evarty/7SegClock/ShiftOut.c

#include <avr/io.h>

#include "ShiftOut.h"

void ShiftOutByte(uint8_t CLKPin, volatile uint8_t *ClockPORT, uint8_t DataPin, volatile uint8_t *DataPORT, uint8_t LatchPin, volatile uint8_t *LatchPORT, uint8_t data){
  
  *LatchPORT &= ~(1 << LatchPin);//Set Latch Pin low
  
  //for all digits in the data variable, bring the clock pin low, then output the correct value on the data pin, then bring the clock pin high, then invert the data pin
  for (int i = 0; i < 8; i++){

    *ClockPORT &= ~(1 << CLKPin);//set clock pin low
    *DataPORT |= (((data >> i) & 0x01) << DataPin);//set data pin to the correct value
    *ClockPORT |= (1 << CLKPin); //set clock pin high
    *DataPORT &= ~(((data >> i) & 0x01) << DataPin);//set data pin to the opposite of previously correct value
    
  }

  *LatchPORT |= (1 << LatchPin);//set latch pin high

}

//same logic as the other, but with more elements.
//Assuming that the data needed to be shifted out is in the correct order, it just goes over the whole array
void ShiftOutMultiByte(uint8_t CLKPin, volatile uint8_t *ClockPORT, uint8_t DataPin, volatile uint8_t *DataPORT, uint8_t LatchPin, volatile uint8_t *LatchPORT, uint8_t *data, uint8_t NumDataByte){

  *LatchPORT &= ~(1 << LatchPin);
  
  for(int i = 0; i < (8 * NumDataByte); i++){
    
    *ClockPORT &= ~(1 << CLKPin);
    *DataPORT |= (((data[i] >> i ) & 0x01 ) << DataPin );
    *ClockPORT |= (1 << CLKPin);
    *DataPORT &= ~(((data[i] >> i ) & 0x01) << DataPin );
    
  }
  
  *LatchPORT |= (1 << LatchPin);

}
