evarty/7SegClock/IIC.c

//All code is pulled pretty much directly from the datasheet with minimal changes
#include <avr/io.h>

void TWIInit(void){
  //set SCL to CPUClock/40
  //For 1MHz clock, 25KHz
  TWSR = 0x00;
  TWBR = 0x0C;
  //enable TWI
  TWCR = (1<<TWEN);
}

void TWIStart(void){
  TWCR = (1<<TWINT) | (1<<TWSTA) | (1<<TWEN);
  while ((TWCR & (1<<TWINT)) == 0);
}

void TWIStop(void){
  TWCR = (1<<TWINT) | (1<<TWSTO) | (1<<TWEN);
}

void TWIWrite(uint8_t u8data){
  TWDR = u8data;
  TWCR = (1<<TWINT) | (1<<TWEN);
  while ((TWCR & (1<<TWINT)) == 0);
}

uint8_t TWIReadACK(void){
  TWCR = (1<<TWINT) | (1<<TWEN) | (1<<TWEA);
  while ((TWCR & (1<<TWINT)) == 0);
  return TWDR;
}

uint8_t TWIReadNACK(void){
  TWCR = (1<<TWINT) | (1<<TWEN);
  while ((TWCR & (1<<TWINT)) == 0);
  return TWDR;
}

uint8_t TWIGetStatus(void){
  uint8_t status;
  status = TWSR & 0xF8;
  return status;
}
